tuxsoft/WeatherStation/images/arrange2.jpg

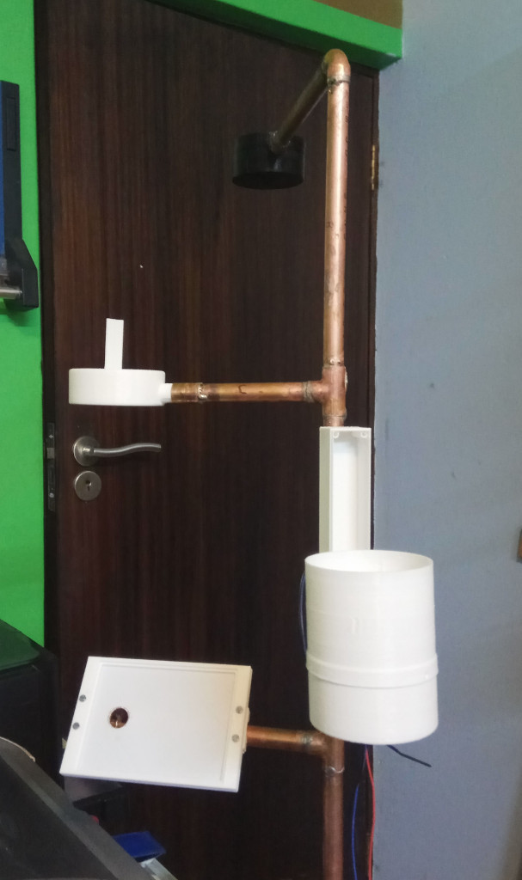
images/arrange2.jpg
