tuxsoft/WeatherStation/images/arrange3.jpg

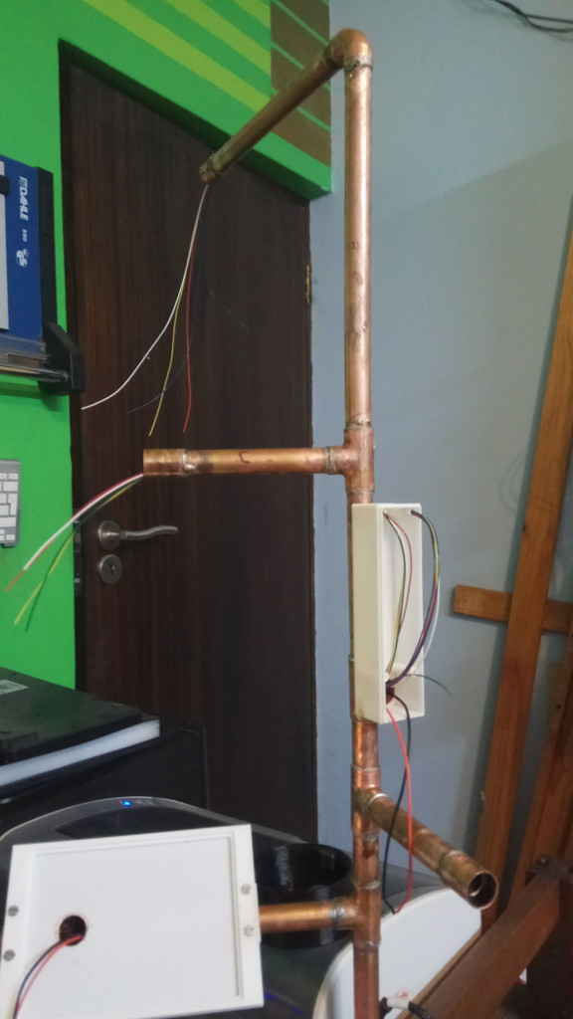
images/arrange3.jpg
