tuxsoft/WeatherStation/images/encoder.jpg

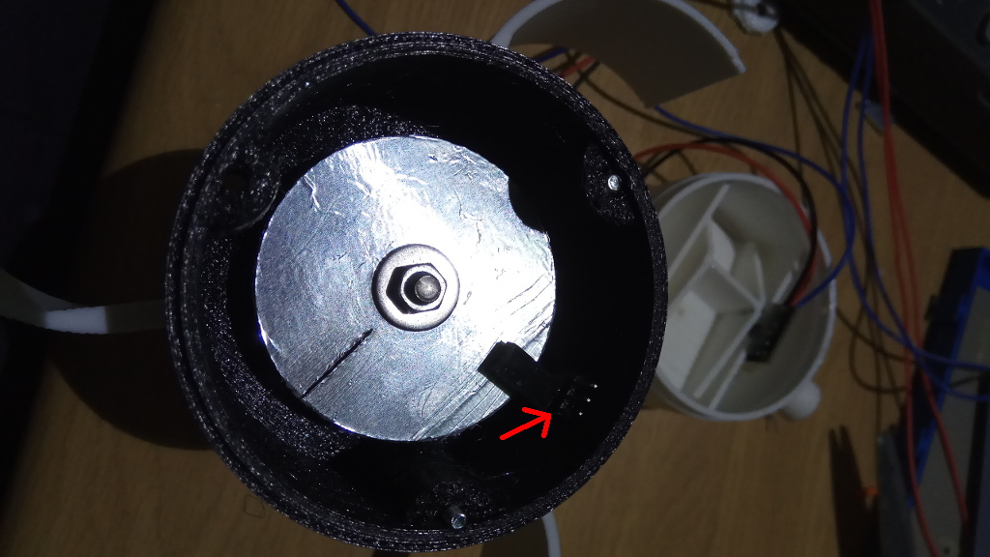
images/encoder.jpg
