tuxsoft/WeatherStation/images/pipe_complete.jpg

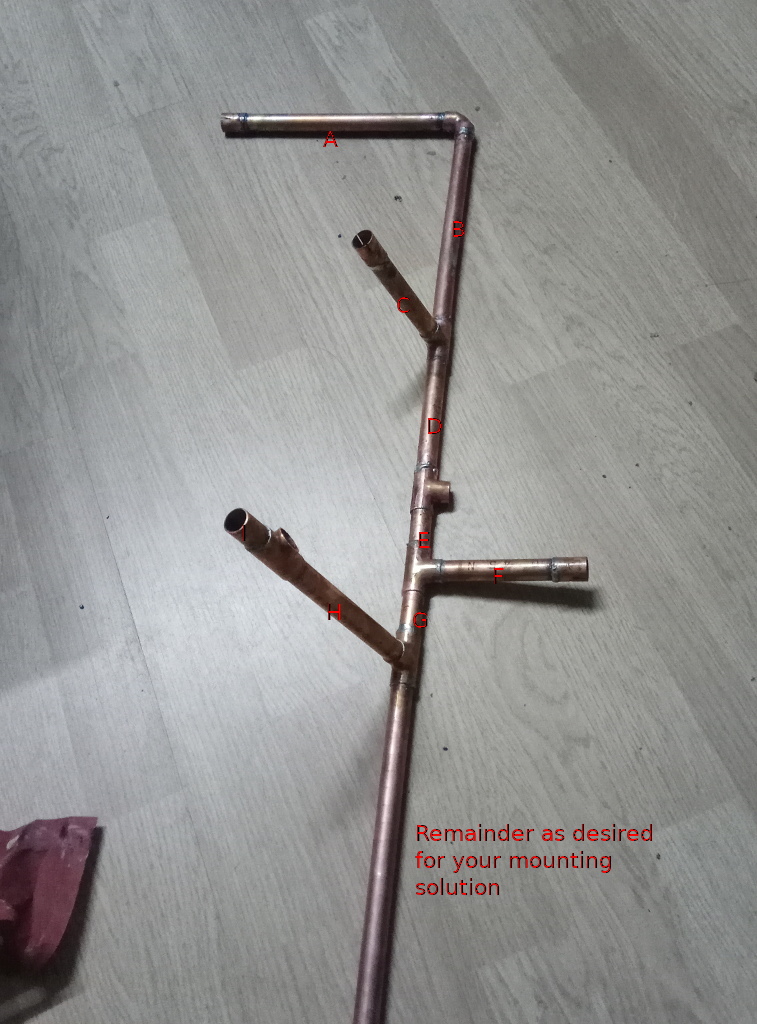
images/pipe_complete.jpg
