tuxsoft/WeatherStation/images/pipes.jpg

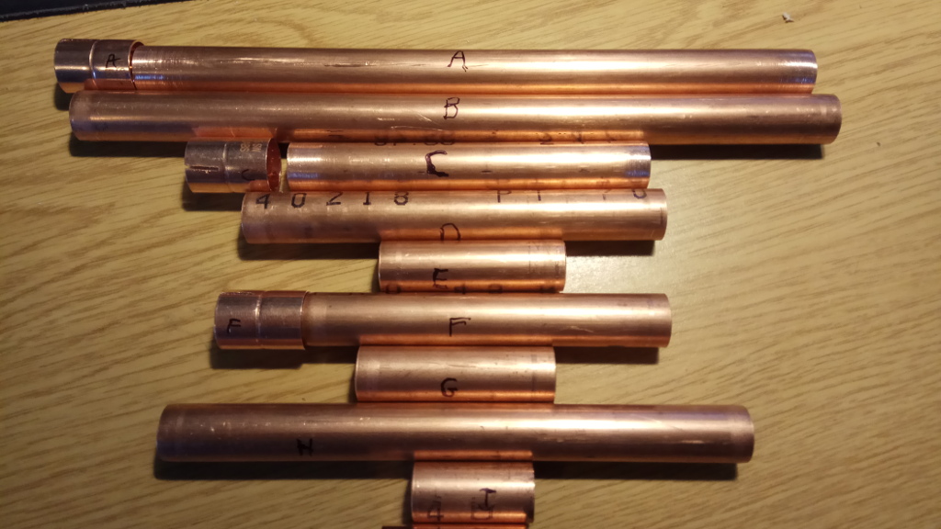
images/pipes.jpg
