tuxsoft/WeatherStation/images/prototype.png

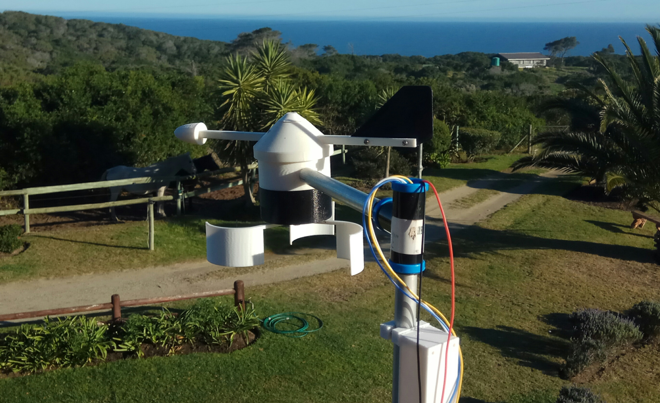
images/prototype.png
