tuxsoft/WeatherStation/images/slot_pipe.jpg

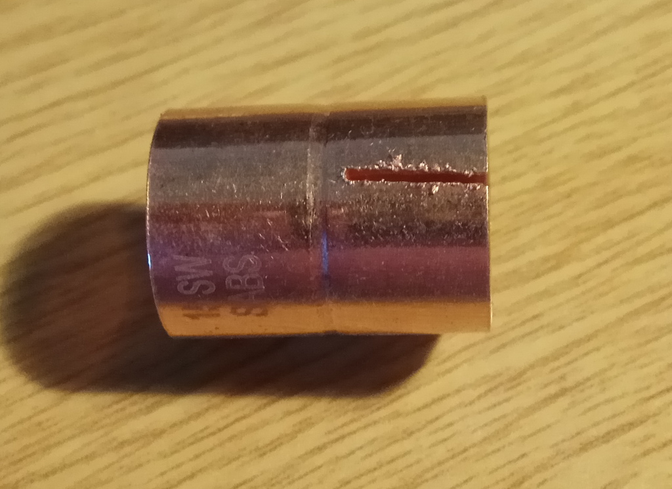
images/slot_pipe.jpg
