tuxsoft/WeatherStation/images/solarbox.png

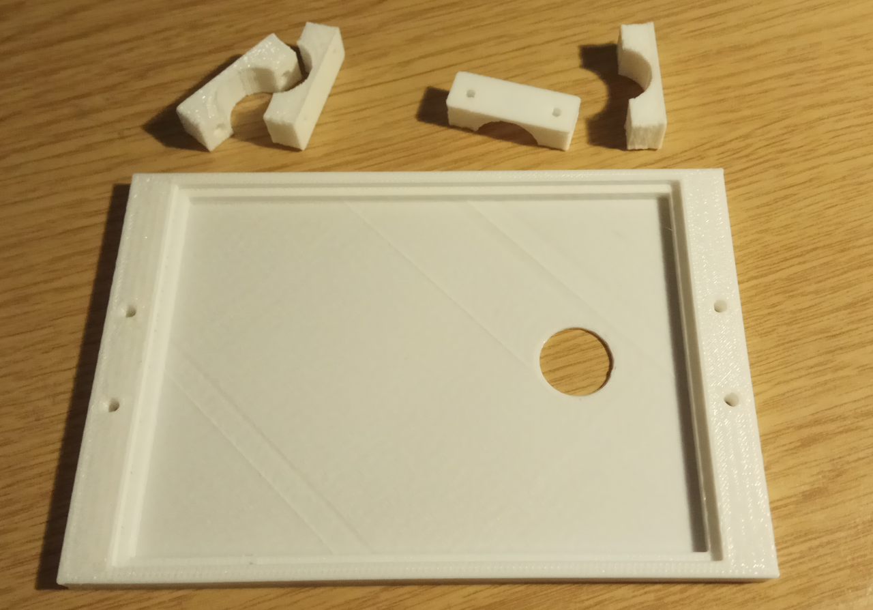
images/solarbox.png
