tuxsoft/WeatherStation/images/tipperOff.jpg

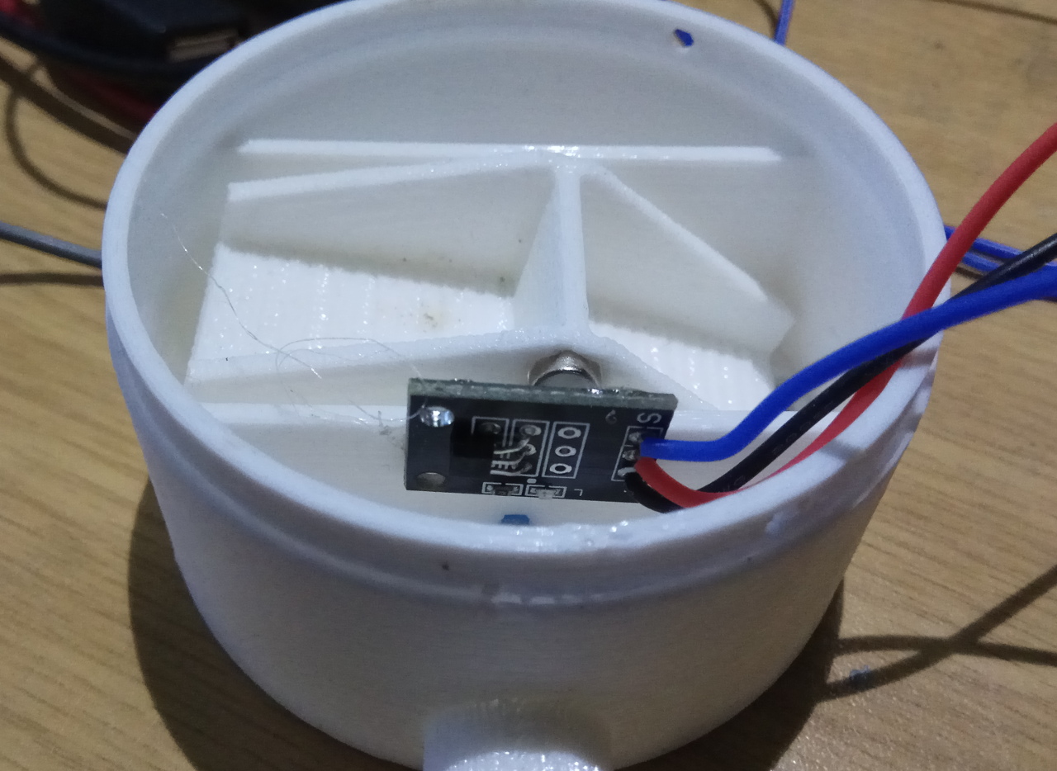
images/tipperOff.jpg
