tuxsoft/WeatherStation/images/tipperOn.jpg

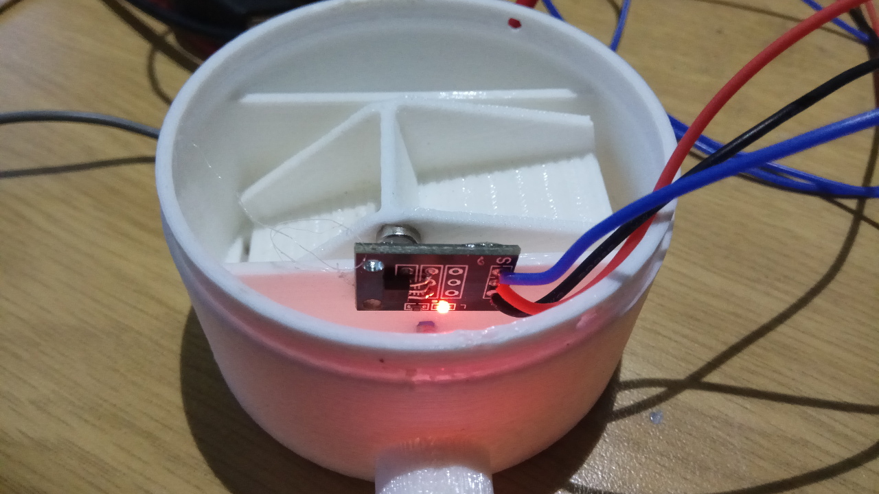
images/tipperOn.jpg
