tuxsoft/WeatherStation/images/parts1.jpg

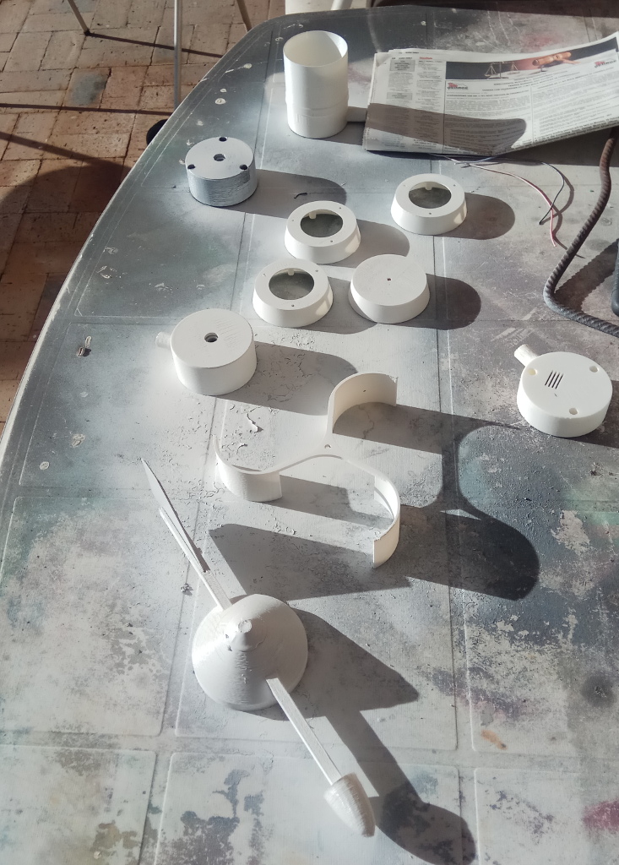
images/parts1.jpg
