tuxsoft/WeatherStation/images/parts2.jpg

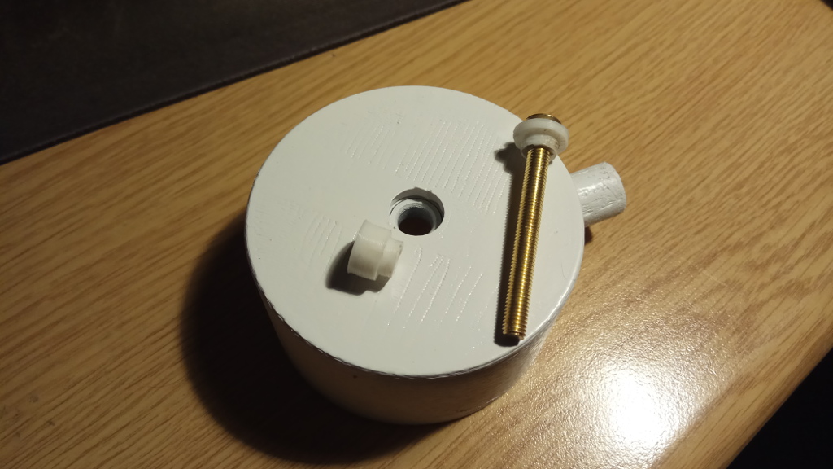
images/parts2.jpg
