tuxsoft/WeatherStation/images/parts3.jpg

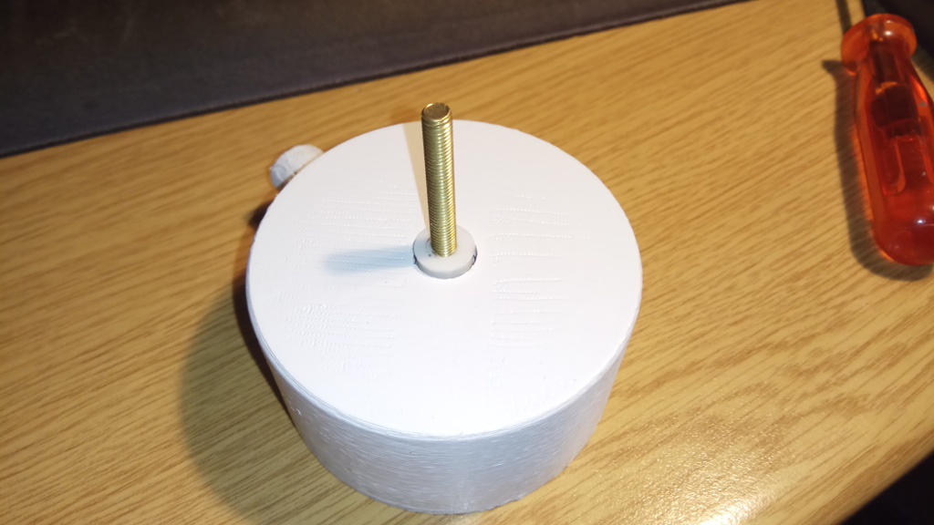
images/parts3.jpg
