tuxsoft/WeatherStation/images/parts5.jpg

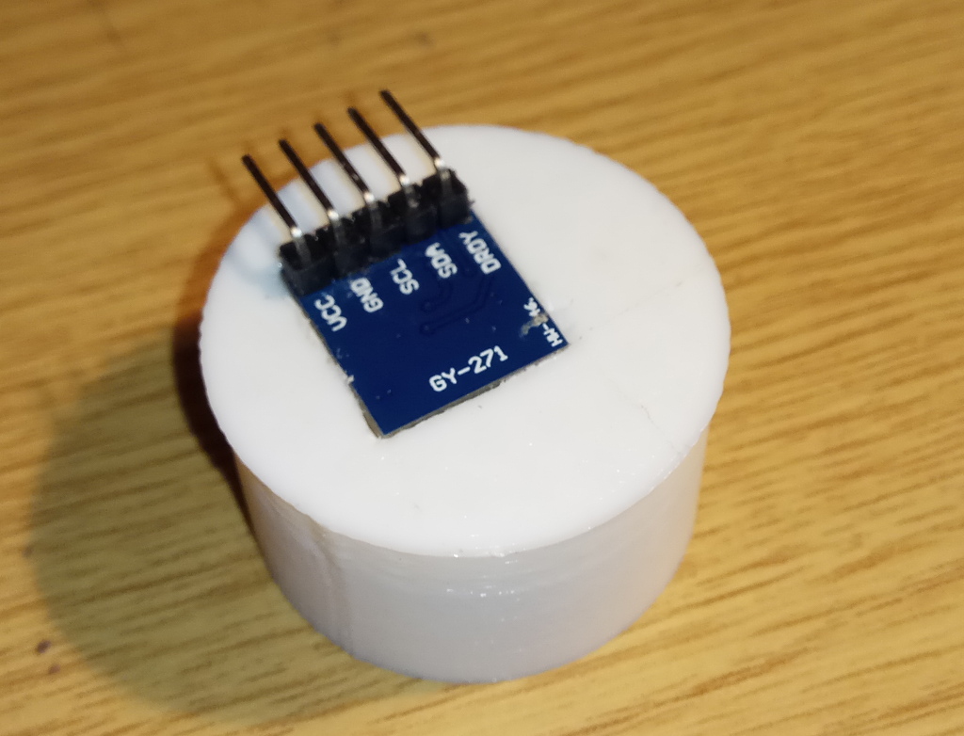
images/parts5.jpg
