tuxsoft/WeatherStation/images/parts6.jpg

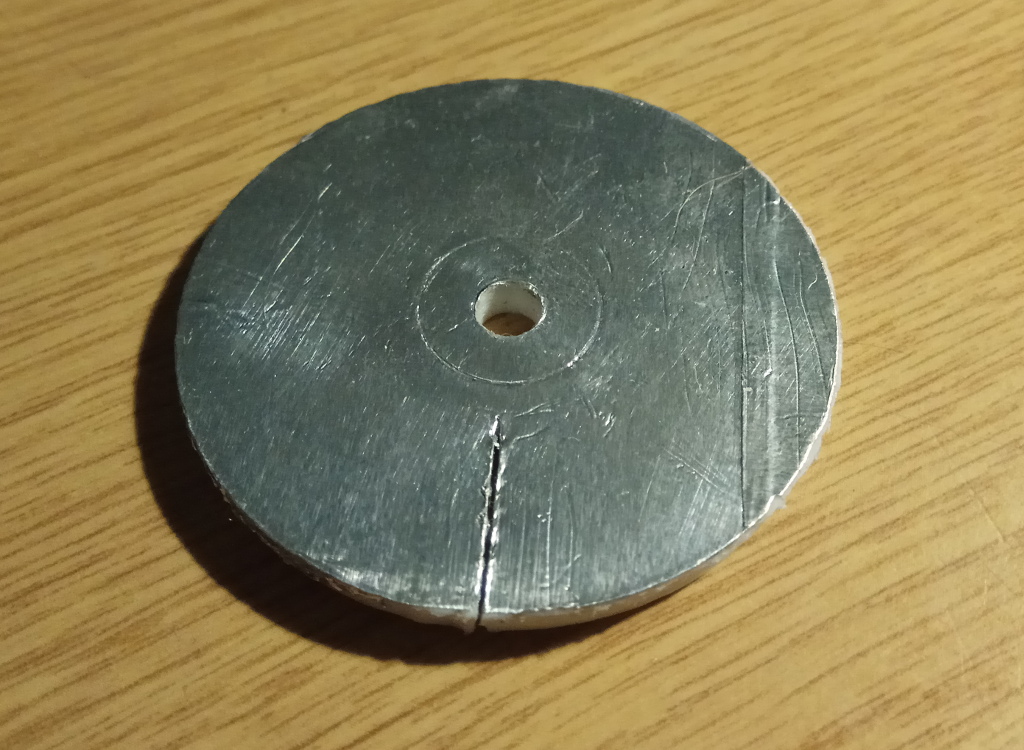
images/parts6.jpg
