tuxsoft/WeatherStation/images/parts7.jpg

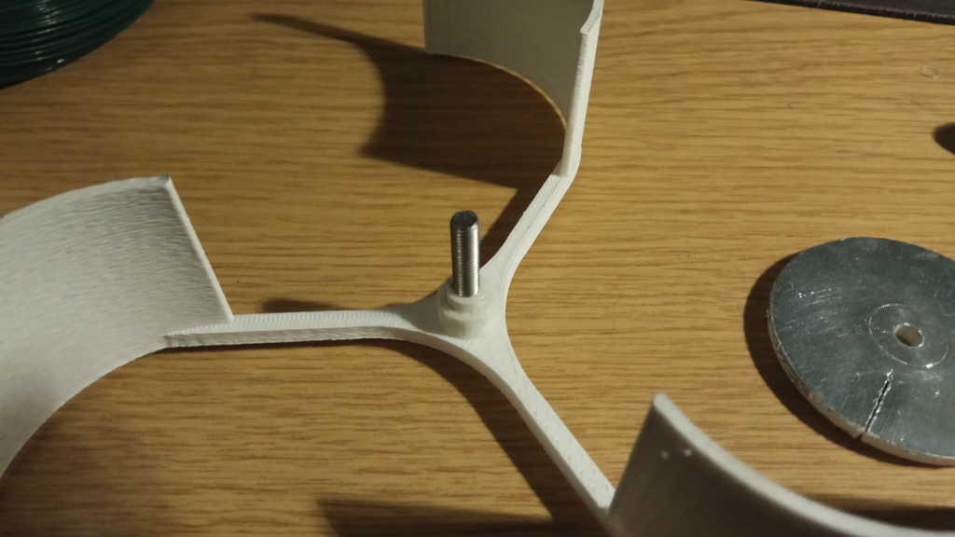
images/parts7.jpg
