tuxsoft/WeatherStation/images/parts8.jpg

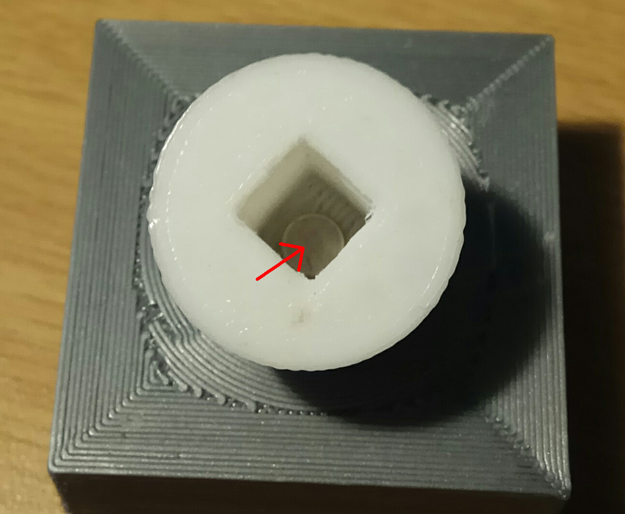
images/parts8.jpg
