tuxsoft/WeatherStation/images/parts10.jpg

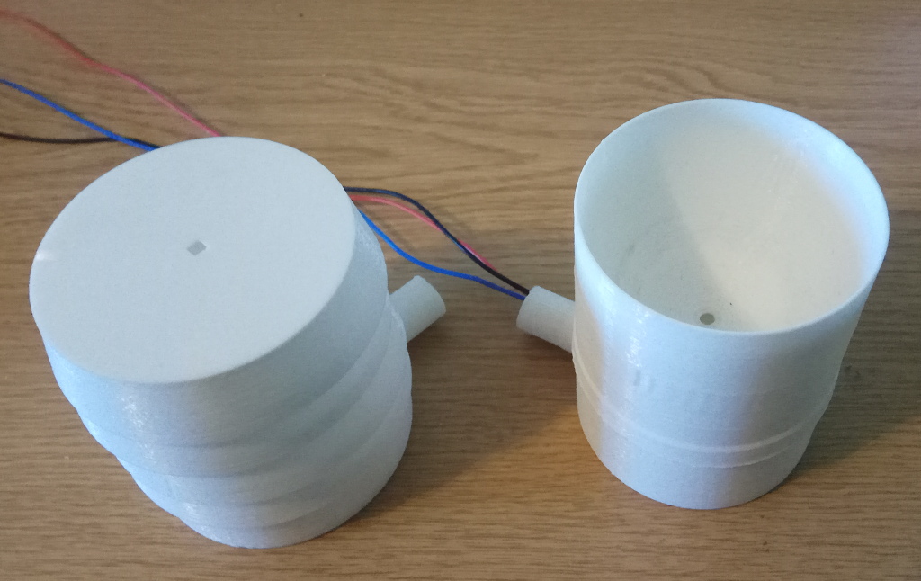
images/parts10.jpg
