tuxsoft/WeatherStation/src/i2creset.cpp

#include <ESP8266WiFi.h>
#include <Wire.h>

/**
 * Based on I2C_ClearBus
 * (http://www.forward.com.au/pfod/ArduinoProgramming/I2C_ClearBus/index.html)
 * (c)2014 Forward Computing and Control Pty. Ltd.
 * NSW Australia, www.forward.com.au
 * This code may be freely used for both private and commerical use
 */

void I2C_Reset()
{
	pinMode (SDA, INPUT_PULLUP); // Make SDA (data) and SCL (clock) pins Inputs with pullup.
	pinMode (SCL, INPUT_PULLUP);

	delay(500);

	if (digitalRead(SCL) == LOW) // Can't become a master
	{
		return;
	}


	boolean SDA_LOW = (digitalRead(SDA) == LOW);  // vi. Check SDA input.
	int clockCount = 20; // > 2x9 clock

	while (SDA_LOW && (clockCount-- > 0))
	{
		// Note: I2C bus is open collector so do NOT drive SCL or SDA high.
		pinMode(SCL, INPUT); // release SCL pullup so that when made output it will be LOW
		pinMode(SCL, OUTPUT); // then clock SCL Low
		delayMicroseconds(10); //  for >5uS
		pinMode(SCL, INPUT); // release SCL LOW
		pinMode(SCL, INPUT_PULLUP); // turn on pullup resistors again
		// do not force high as slave may be holding it low for clock stretching.
		delayMicroseconds(10); //  for >5uS

		// The >5uS is so that even the slowest I2C devices are handled.
		boolean SCL_LOW = (digitalRead(SCL) == LOW); // Check if SCL is Low.
		int counter = 20;
		while (SCL_LOW && (counter-- > 0))  //  loop waiting for SCL to become High only wait 2sec.
		{
			delay(100);
			SCL_LOW = (digitalRead(SCL) == LOW);
		}
		if (SCL_LOW)  // still low after 2 sec error
		{
			return;
		}
		SDA_LOW = (digitalRead(SDA) == LOW); //   and check SDA input again and loop
	}
	if (SDA_LOW)  // still low
	{
		return;
	}

	// else pull SDA line low for Start or Repeated Start
	pinMode(SDA, INPUT); // remove pullup.
	pinMode(SDA, OUTPUT);  // and then make it LOW i.e. send an I2C Start or Repeated start control.
	// When there is only one I2C master a Start or Repeat Start has the same function as a Stop and clears the bus.
	/// A Repeat Start is a Start occurring after a Start with no intervening Stop.
	delayMicroseconds(10); // wait >5uS
	pinMode(SDA, INPUT); // remove output low
	pinMode(SDA, INPUT_PULLUP); // and make SDA high i.e. send I2C STOP control.
	delayMicroseconds(10); // x. wait >5uS
	pinMode(SDA, INPUT); // and reset pins as tri-state inputs which is the default state on reset
	pinMode(SCL, INPUT);
}
