tuxsoft/WeatherStation/src/ssid.h

// Remove this include and add your wifi details
#include "private_ssid.h"

#ifndef __SSID_H__
#define __SSID_H__

// Fill in your details here 
const char* ssid = "weather";
const char* passwd = "4free" // ; Syntax error to force you to to this
#endif
